bcndynamics/MaduixaCNC/03.Pictures/2sides-corner-CNC.png

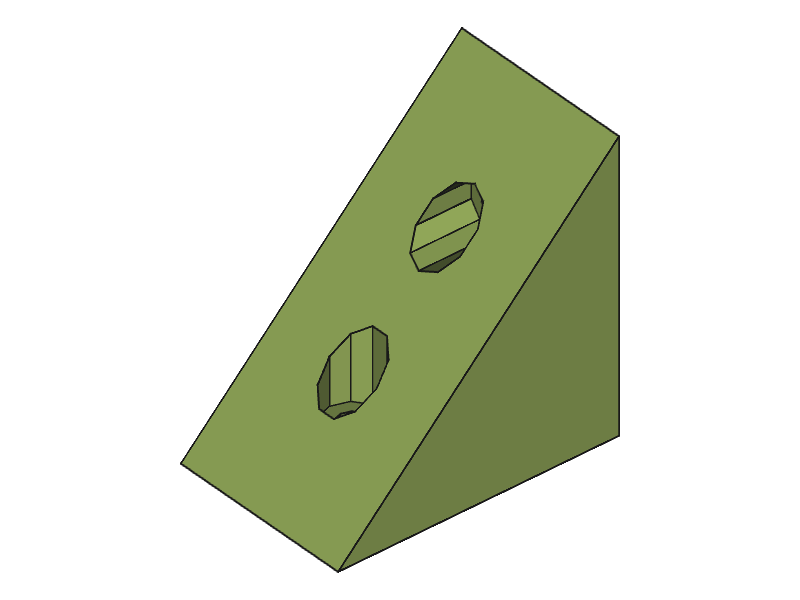
03.Pictures/2sides-corner-CNC.png
