bcndynamics/MaduixaCNC/03.Pictures/3sides-corner-CNC.png

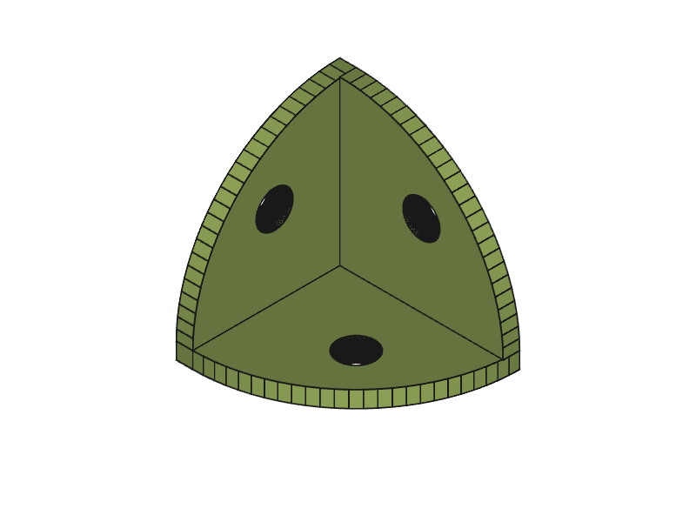
03.Pictures/3sides-corner-CNC.png
