bcndynamics/MaduixaCNC/03.Pictures/bed-holder-CNC.png

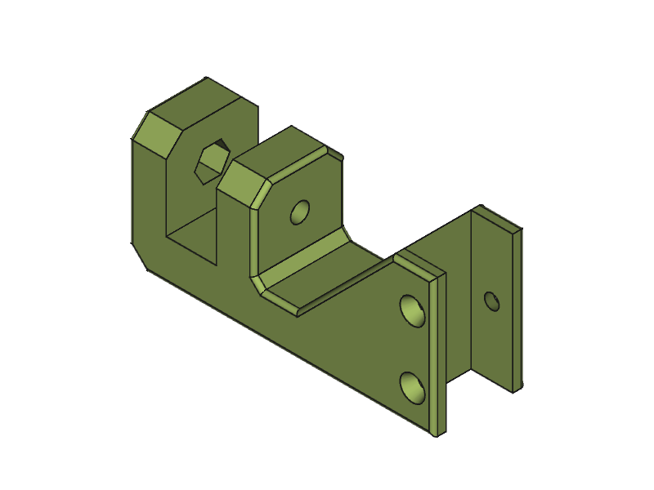
03.Pictures/bed-holder-CNC.png
