bcndynamics/MaduixaCNC/03.Pictures/lm8uu-holder-CNC.png

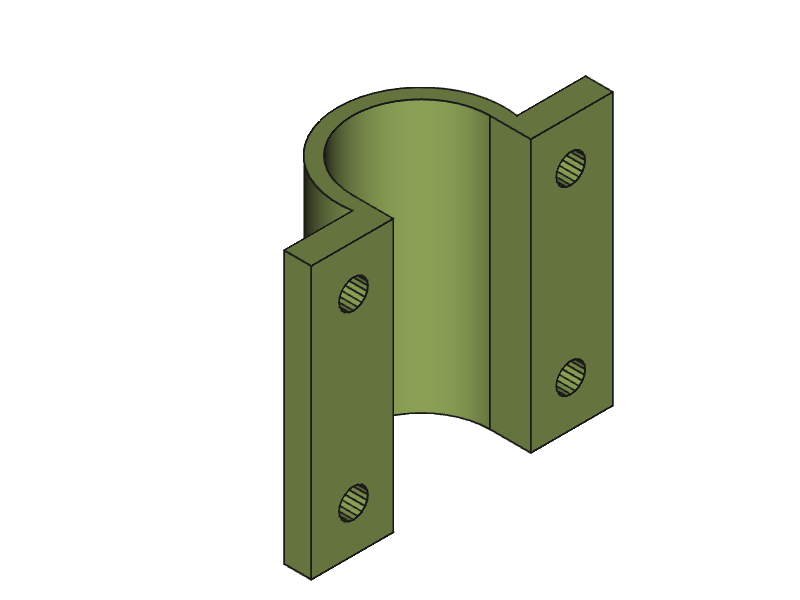
03.Pictures/lm8uu-holder-CNC.png
