bcndynamics/MaduixaCNC/03.Pictures/maduixacnc001.jpg

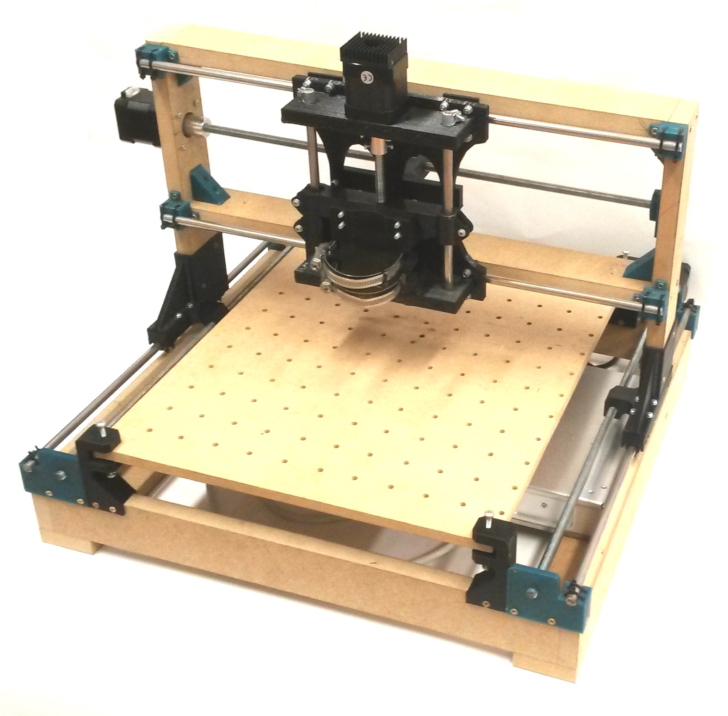
03.Pictures/maduixacnc001.jpg
