bcndynamics/MaduixaCNC/03.Pictures/maduixacnc002.jpg

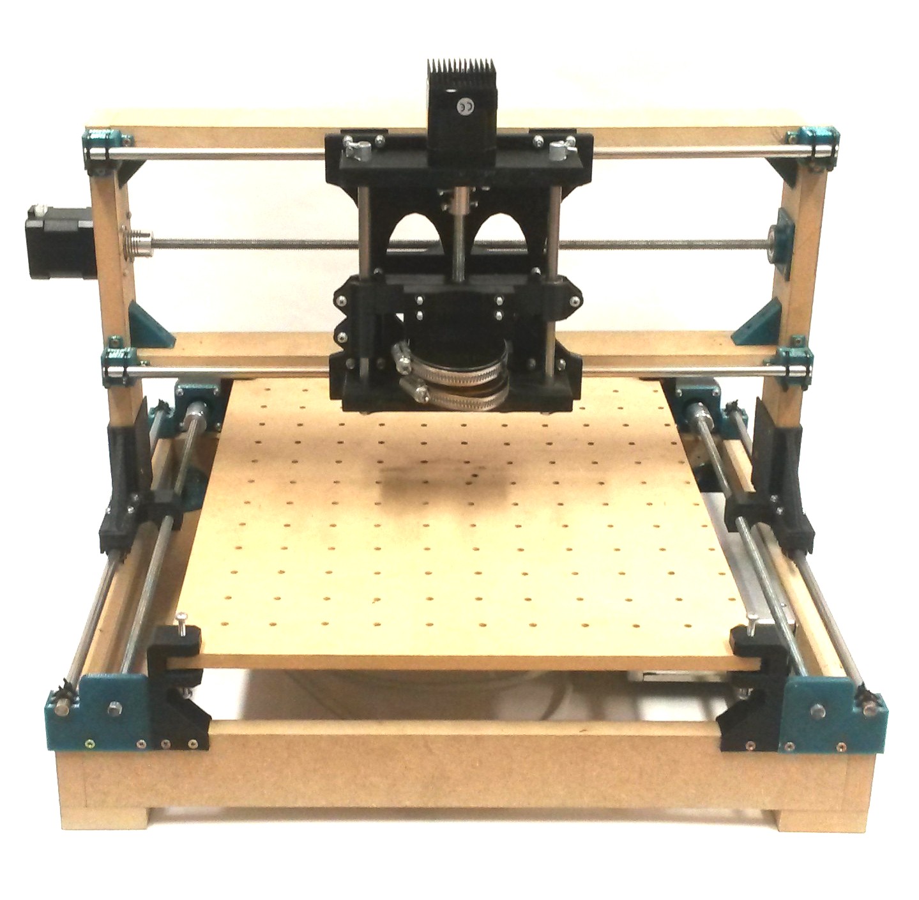
03.Pictures/maduixacnc002.jpg
