bcndynamics/MaduixaCNC/03.Pictures/maduixacnc003.jpg

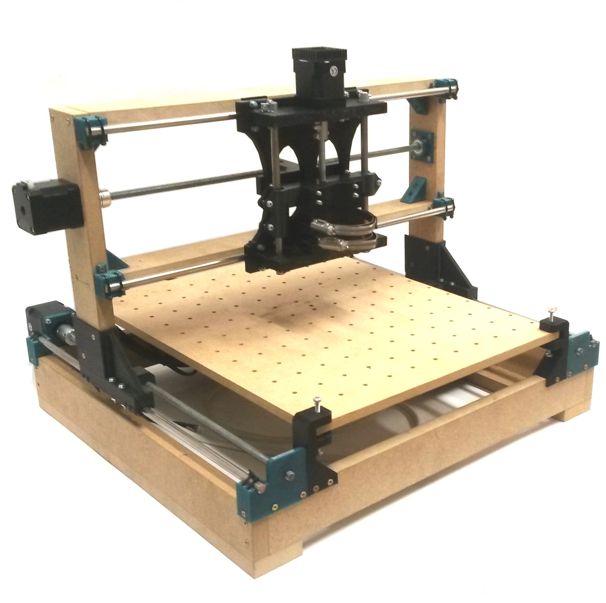
03.Pictures/maduixacnc003.jpg
