bcndynamics/MaduixaCNC/03.Pictures/MaduixaCNC-back-r.png

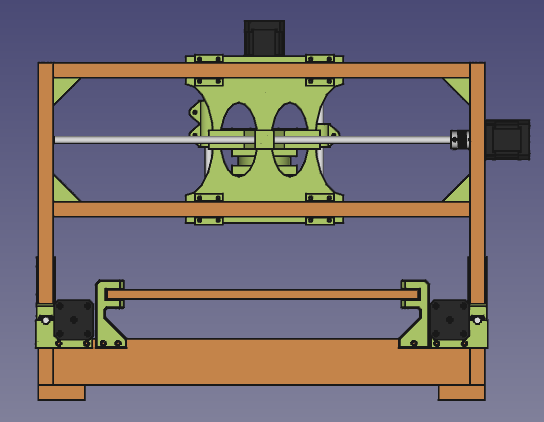
03.Pictures/MaduixaCNC-back-r.png
