bcndynamics/MaduixaCNC/03.Pictures/MaduixaCNC-back.png

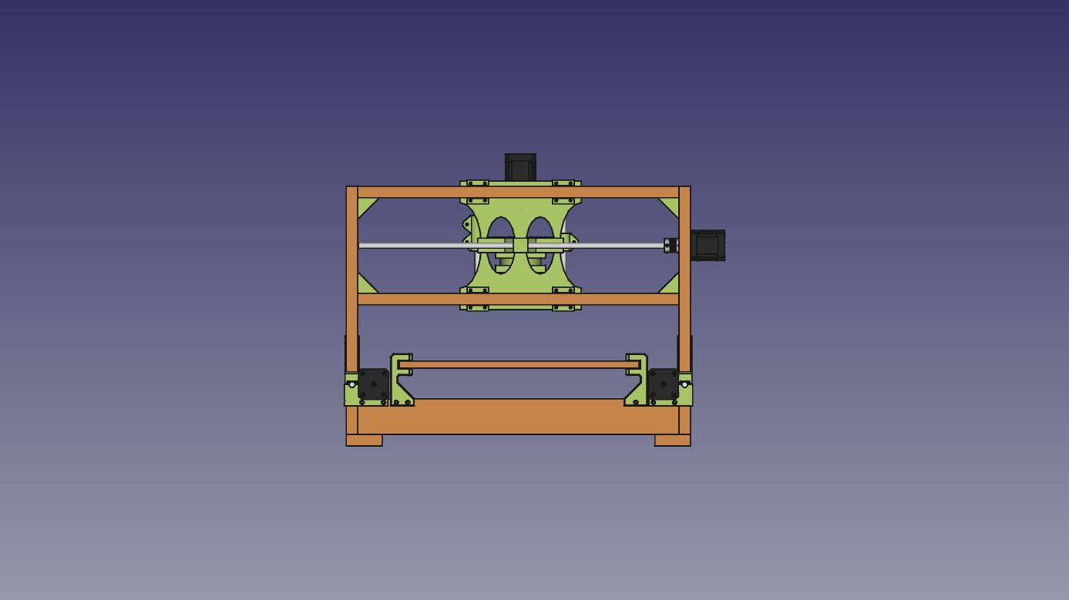
03.Pictures/MaduixaCNC-back.png
