bcndynamics/MaduixaCNC/03.Pictures/MaduixaCNC-bottom-r.png

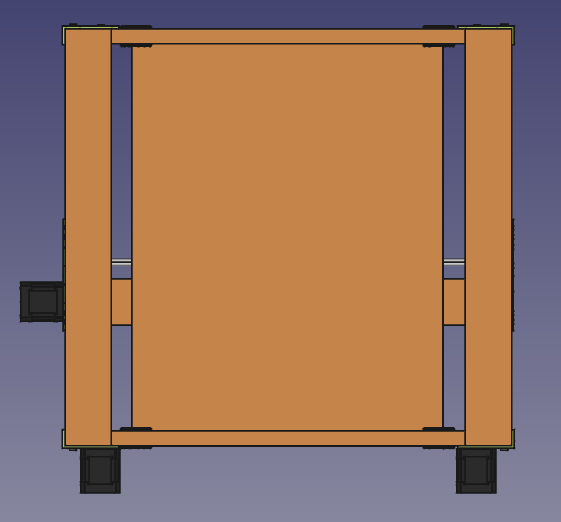
03.Pictures/MaduixaCNC-bottom-r.png
