bcndynamics/MaduixaCNC/03.Pictures/MaduixaCNC-bottom.png

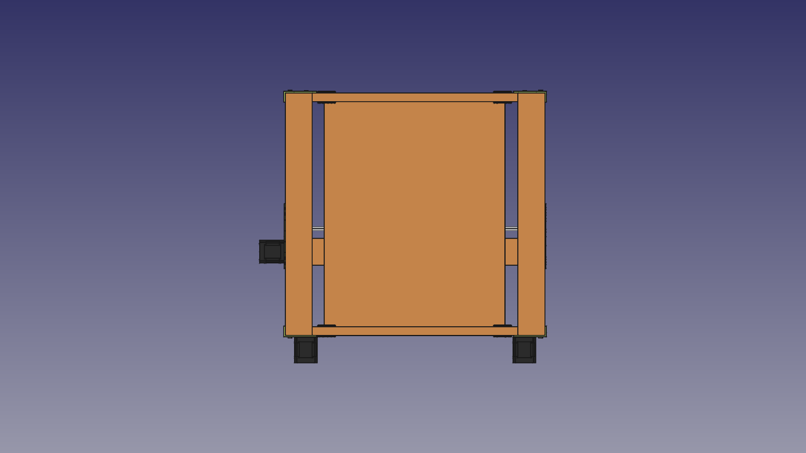
03.Pictures/MaduixaCNC-bottom.png
