bcndynamics/MaduixaCNC/03.Pictures/MaduixaCNC-front.png

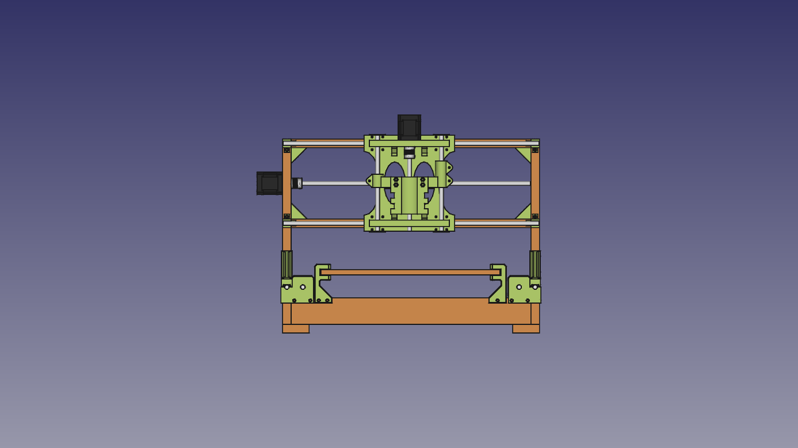
03.Pictures/MaduixaCNC-front.png
