bcndynamics/MaduixaCNC/03.Pictures/MaduixaCNC-left-r.png

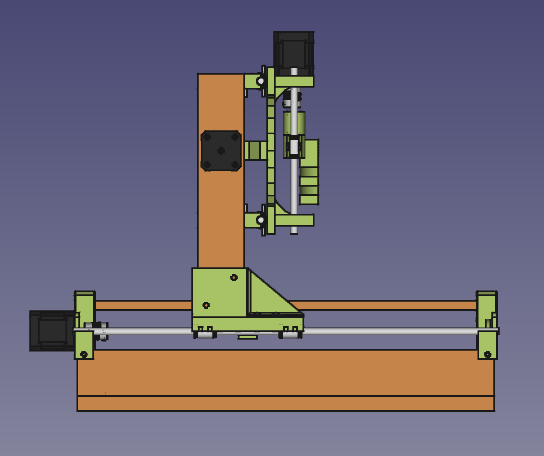
03.Pictures/MaduixaCNC-left-r.png
