bcndynamics/MaduixaCNC/03.Pictures/MaduixaCNC-right-r.png

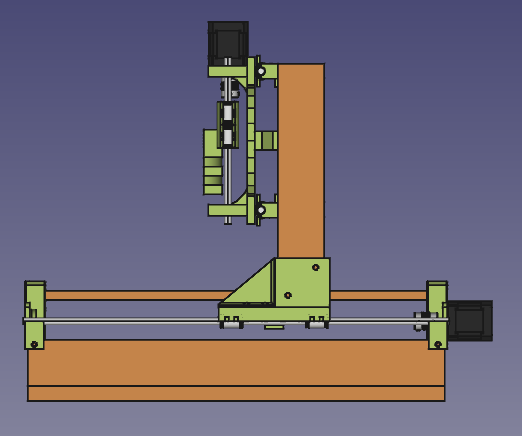
03.Pictures/MaduixaCNC-right-r.png
