bcndynamics/MaduixaCNC/03.Pictures/MaduixaCNC-top-r.png

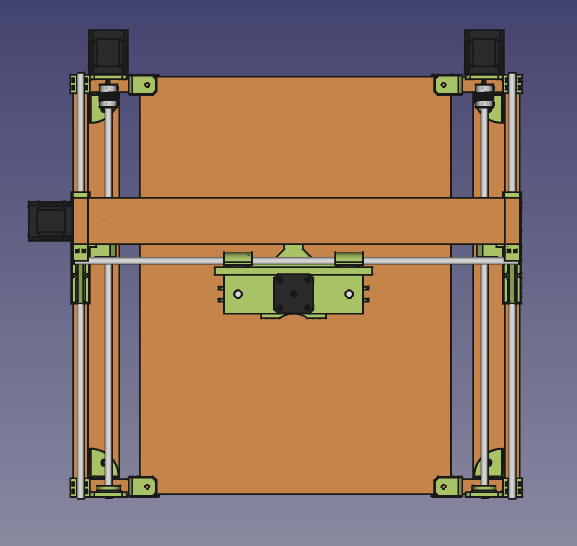
03.Pictures/MaduixaCNC-top-r.png
