bcndynamics/MaduixaCNC/03.Pictures/MaduixaCNC-transpa.png

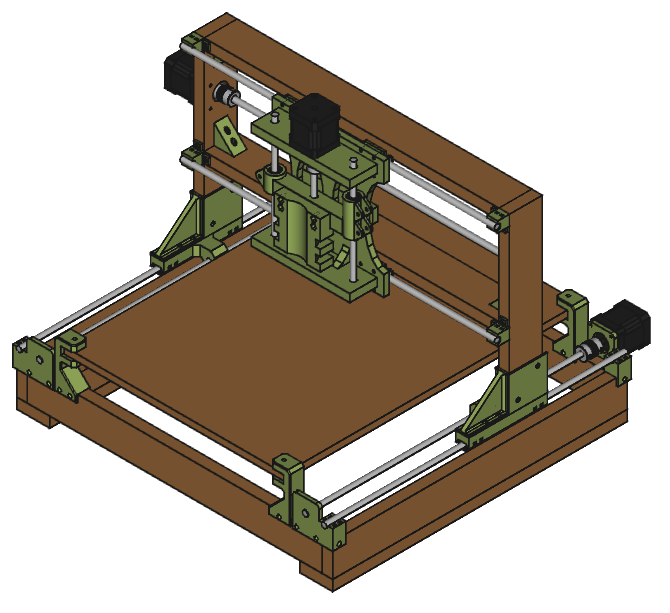
03.Pictures/MaduixaCNC-transpa.png
