bcndynamics/MaduixaCNC/03.Pictures/MaduixaCNC-white.png

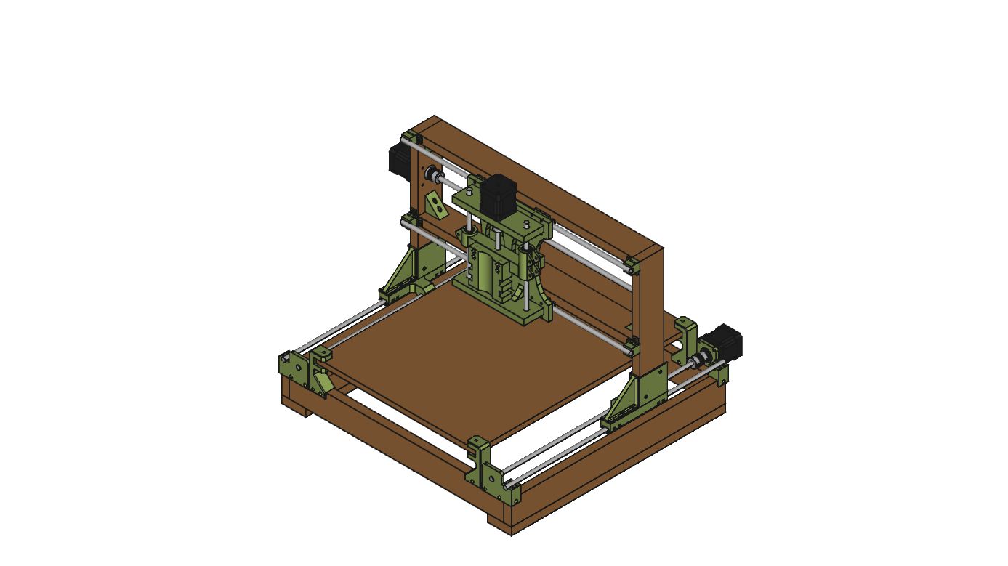
03.Pictures/MaduixaCNC-white.png
