bcndynamics/MaduixaCNC/03.Pictures/universal-holder-CNC.png

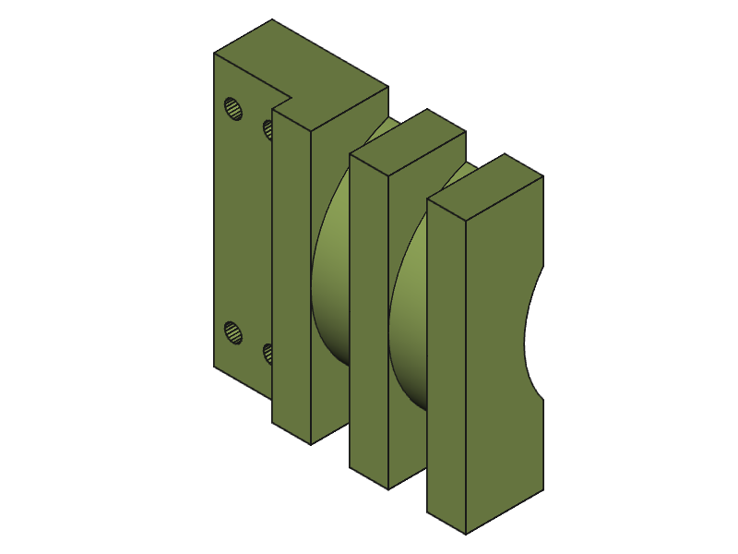
03.Pictures/universal-holder-CNC.png
