bcndynamics/MaduixaCNC/03.Pictures/x-carriage-CNC.png

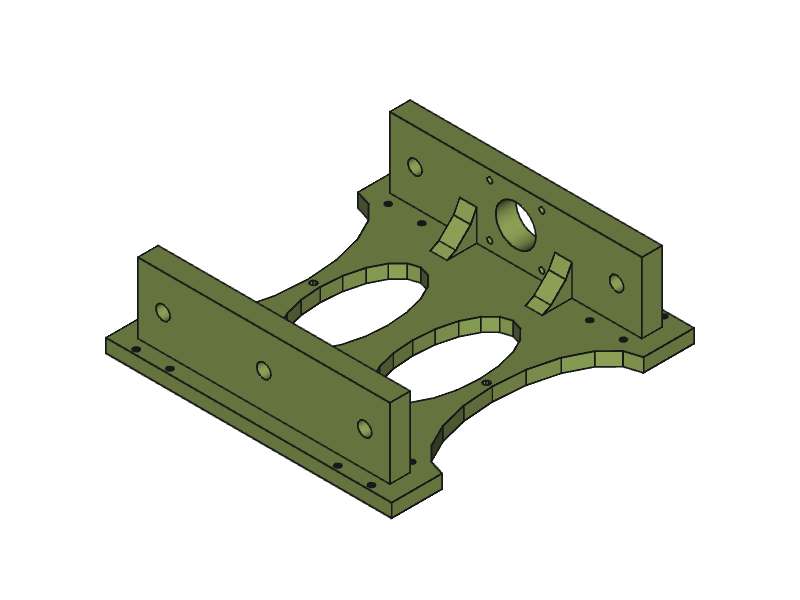
03.Pictures/x-carriage-CNC.png
