bcndynamics/MaduixaCNC/03.Pictures/x-corner-CNC-A.png

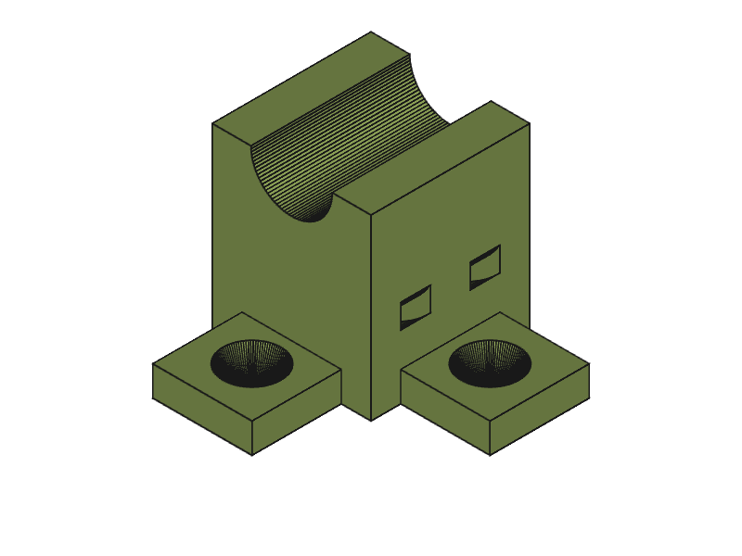
03.Pictures/x-corner-CNC-A.png
