bcndynamics/MaduixaCNC/03.Pictures/x-corner-CNC-B.png

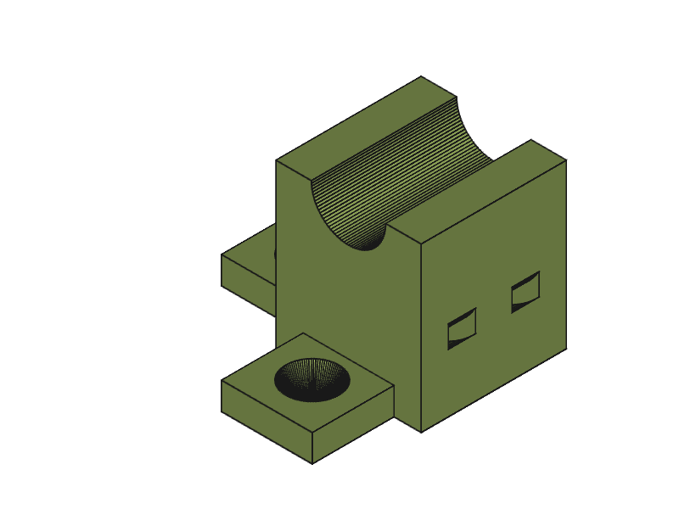
03.Pictures/x-corner-CNC-B.png
