bcndynamics/MaduixaCNC/03.Pictures/x-end-idler-CNC.png

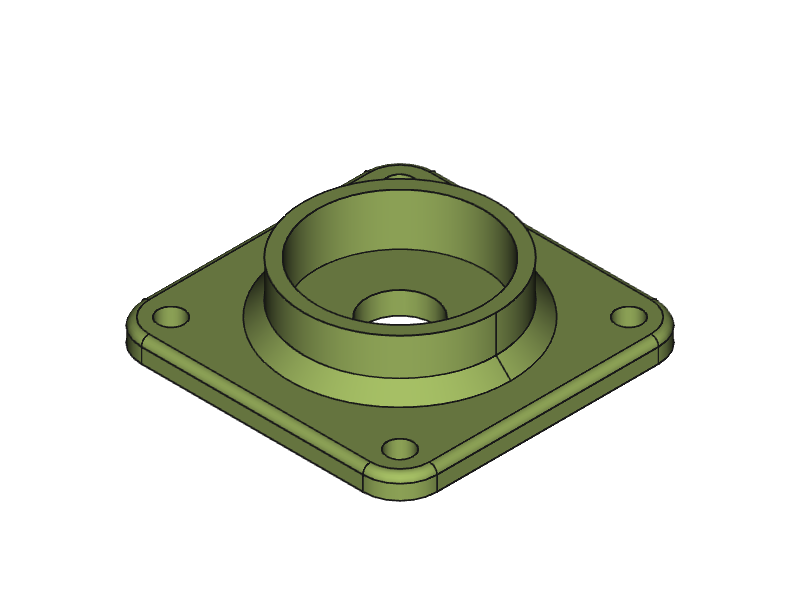
03.Pictures/x-end-idler-CNC.png
