bcndynamics/MaduixaCNC/03.Pictures/y-carriage-CNC.png

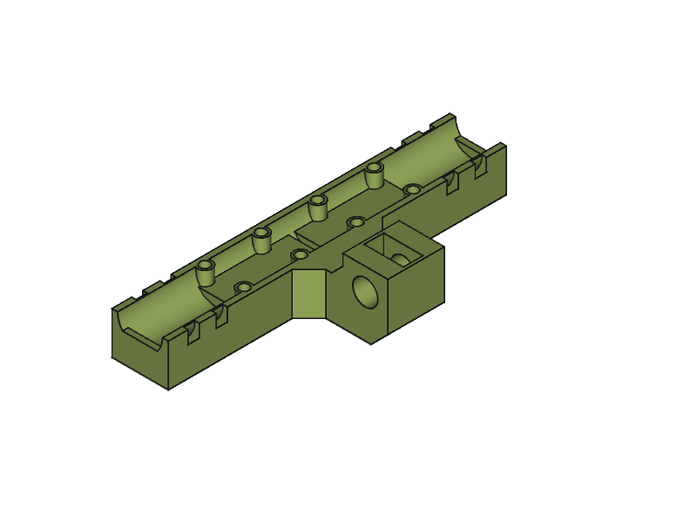
03.Pictures/y-carriage-CNC.png
