bcndynamics/MaduixaCNC/03.Pictures/y-end-idler-CNC-right.png

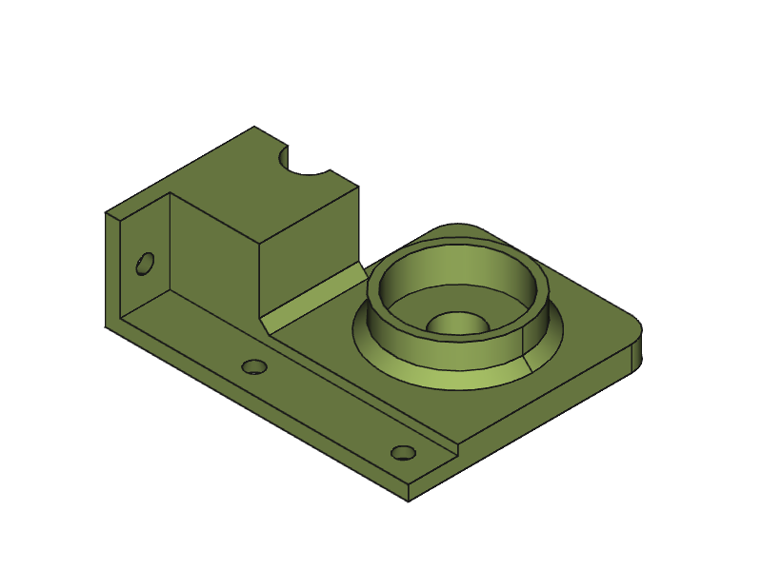
03.Pictures/y-end-idler-CNC-right.png
