bcndynamics/MaduixaCNC/03.Pictures/y-triangle-CNC.png

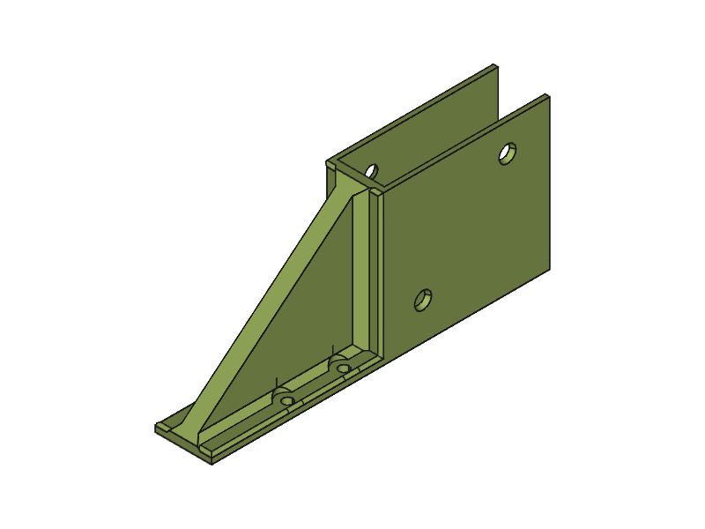
03.Pictures/y-triangle-CNC.png
