bcndynamics/MaduixaCNC/02.STLs/z-carriage-CNC.stl

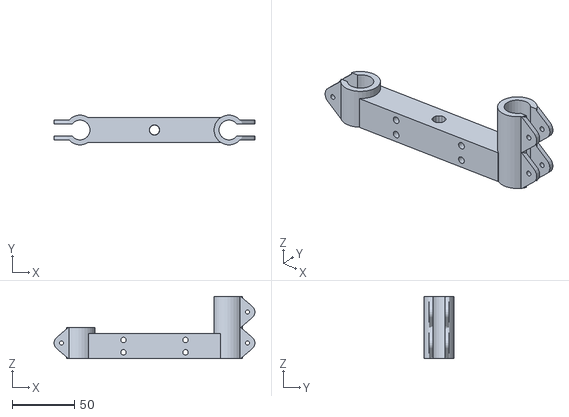
[picture p43: CAD file, 2015-08-28]
02.STLs/z-carriage-CNC.stl
162.0 x 23.9 x 50.0
