bcndynamics/MaduixaCNC/02.STLs/universal-holder-CNC.stl

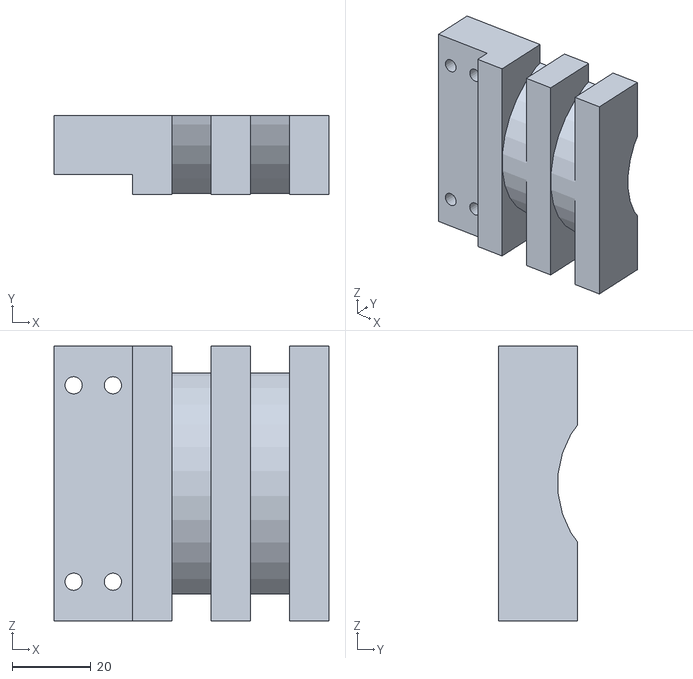
[picture p44: CAD file, 2015-08-28]
02.STLs/universal-holder-CNC.stl
70.0 x 20.0 x 70.0
